semianalog/noisesource/images/high-grey.jpg

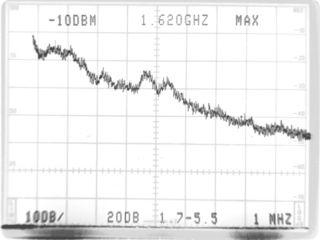
images/high-grey.jpg
