semianalog/noisesource/images/wideband.jpg

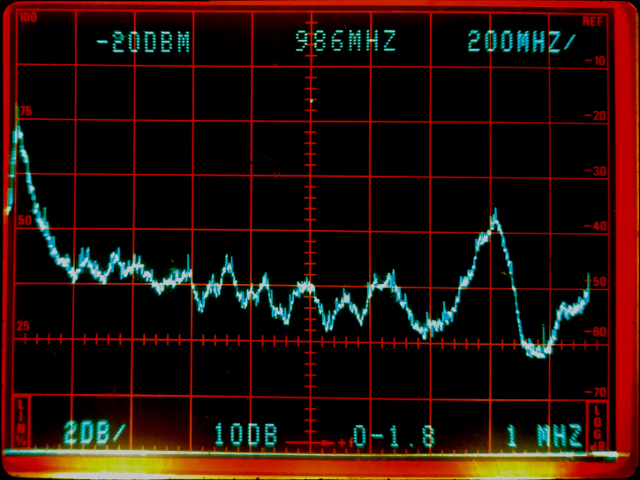
images/wideband.jpg
