semianalog/noisesource/renders/F_Cu.png

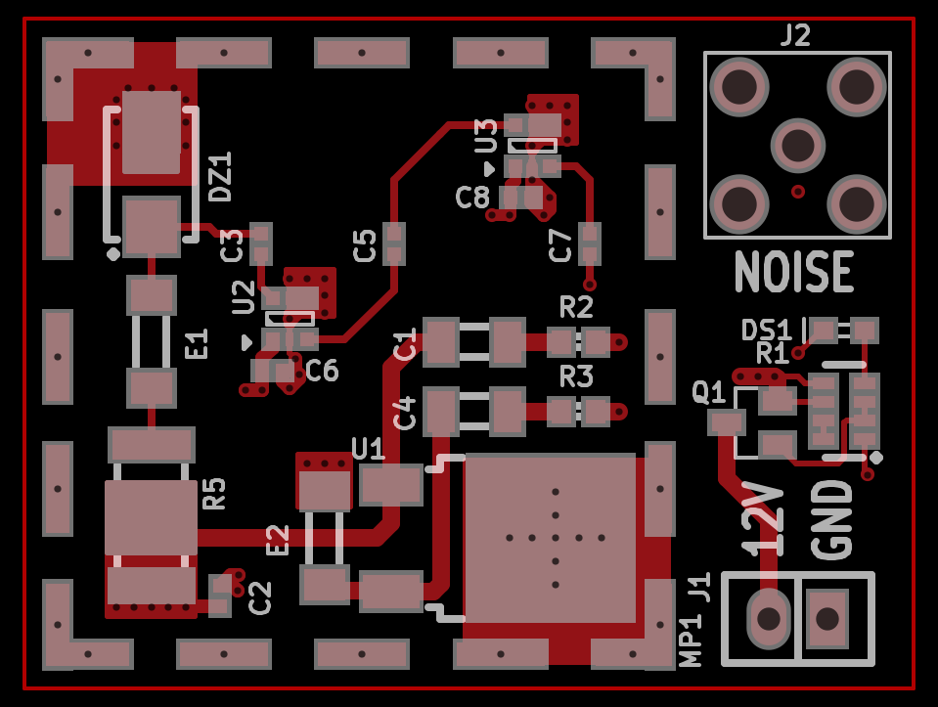
renders/F_Cu.png
