semianalog/noisesource/renders/In1_Cu.png

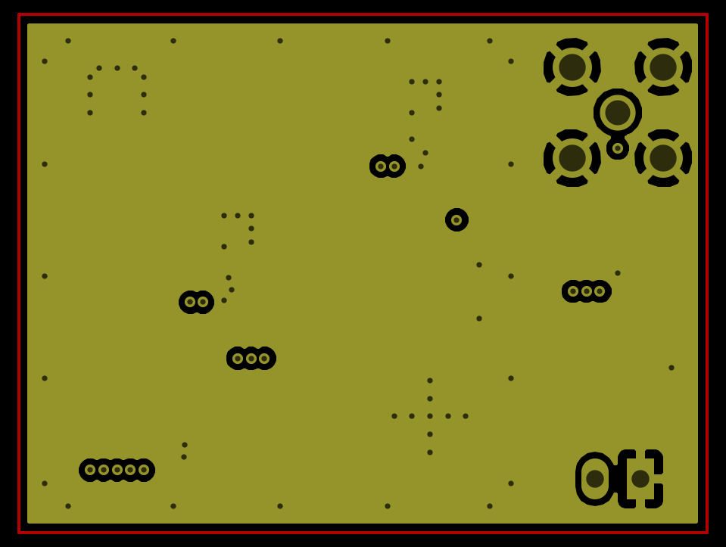
renders/In1_Cu.png
