semianalog/noisesource/renders/In2_Cu.png

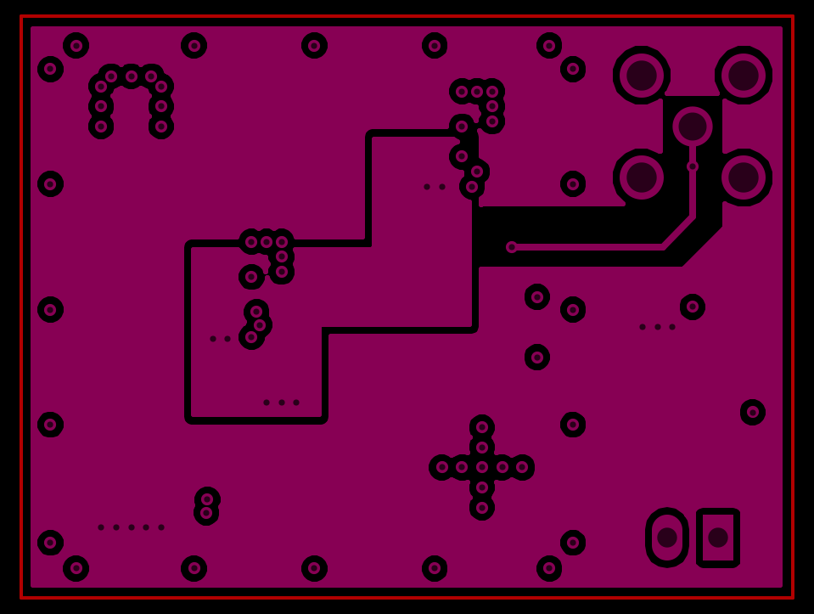
renders/In2_Cu.png
